telzo2000/meishi001/img/img00002.jpg

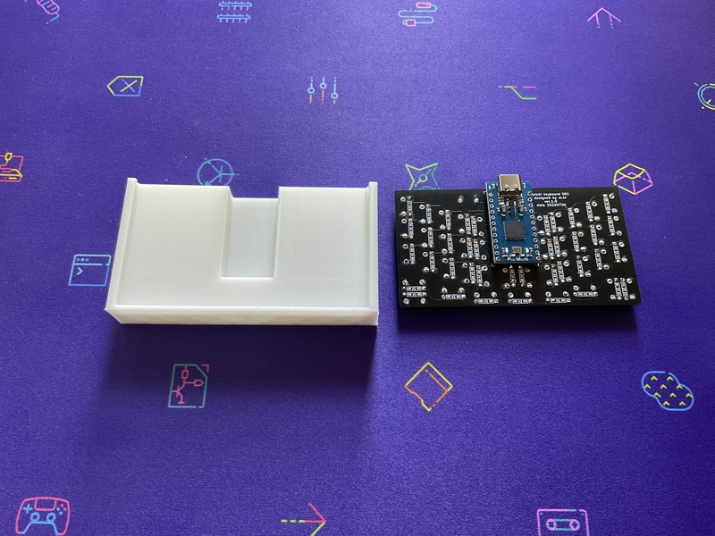
img/img00002.jpg
