telzo2000/meishi001/img/img00003.jpg

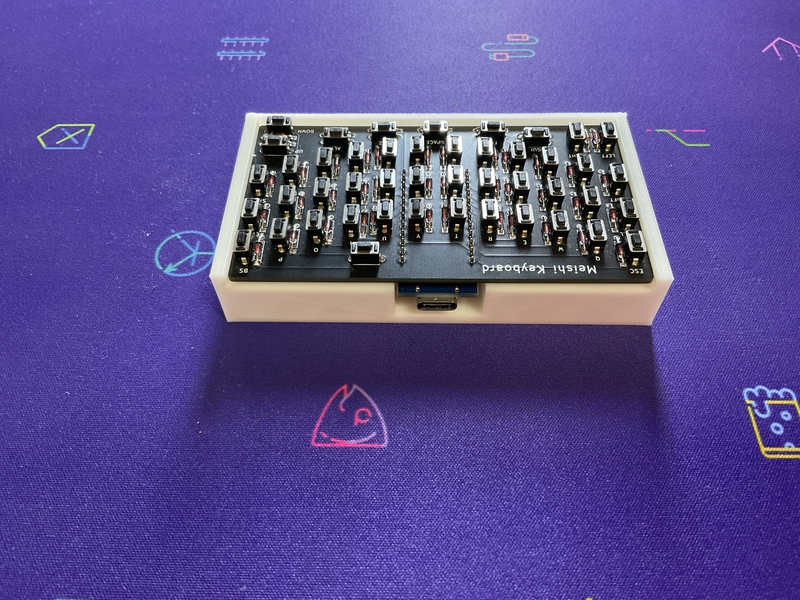
img/img00003.jpg
