telzo2000/meishi001/img/img00005.jpg

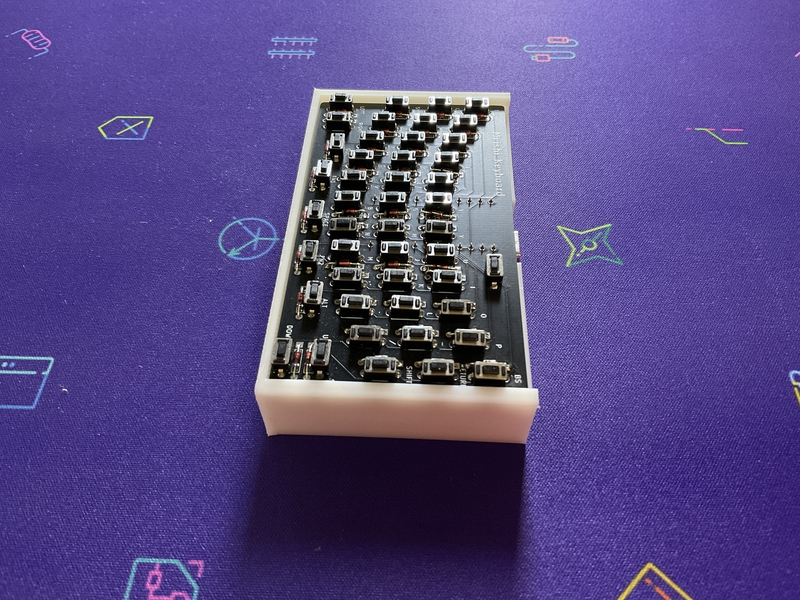
img/img00005.jpg
