telzo2000/meishi001/img/img00006.jpg

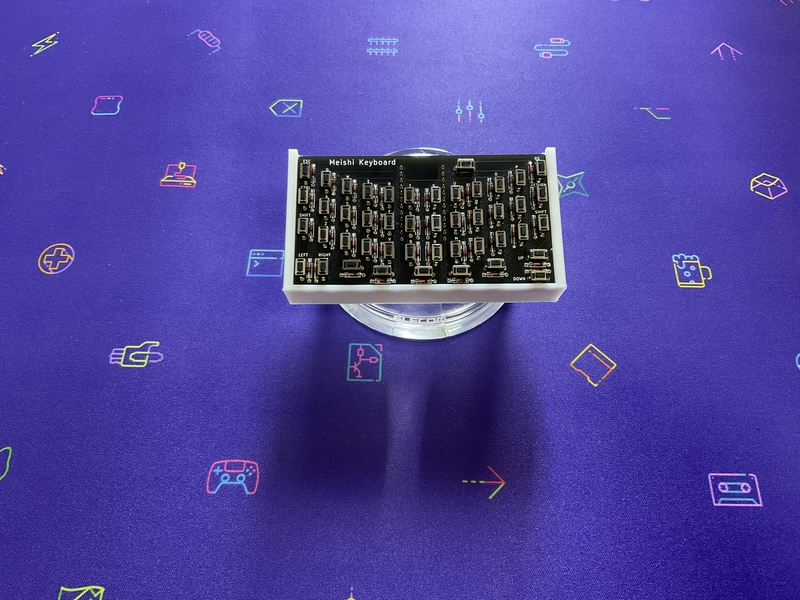
img/img00006.jpg
