telzo2000/meishi001/img/img00007.jpg

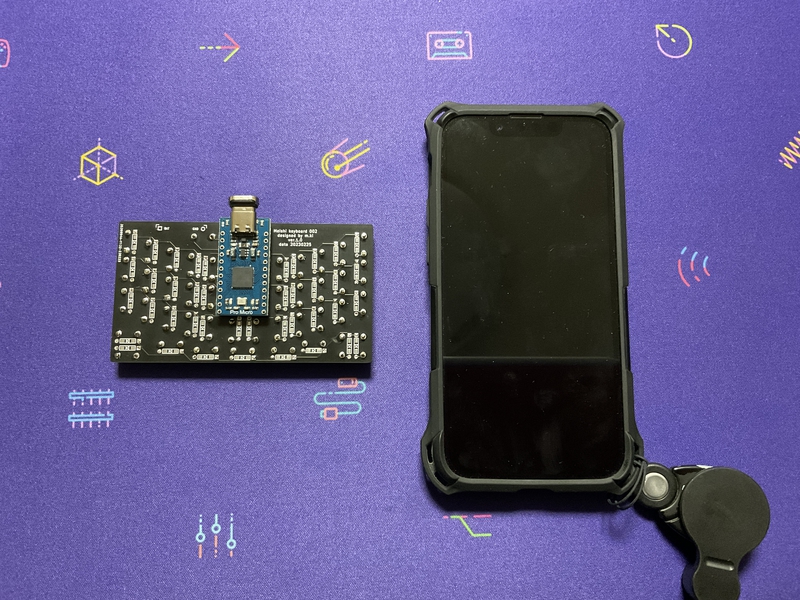
img/img00007.jpg
