telzo2000/meishi001/img/img00008.jpg

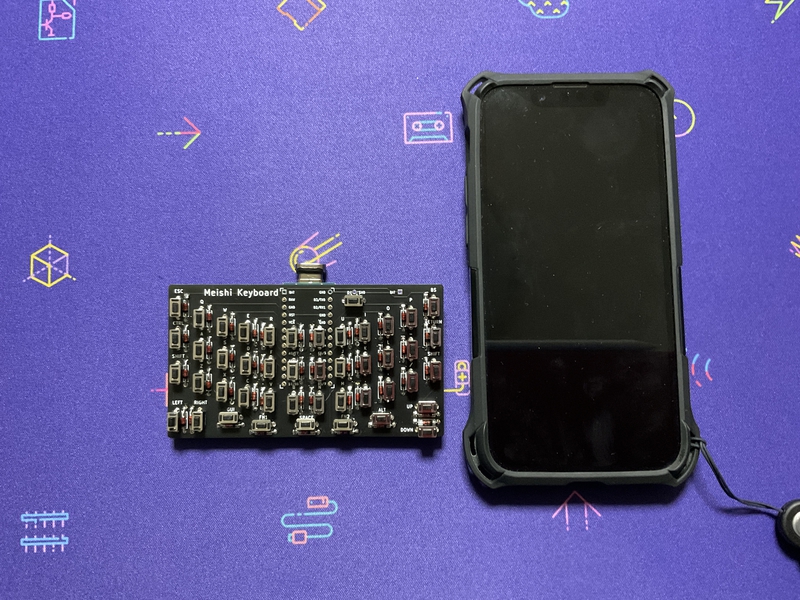
img/img00008.jpg
