telzo2000/meishi001/img/img00009.jpg

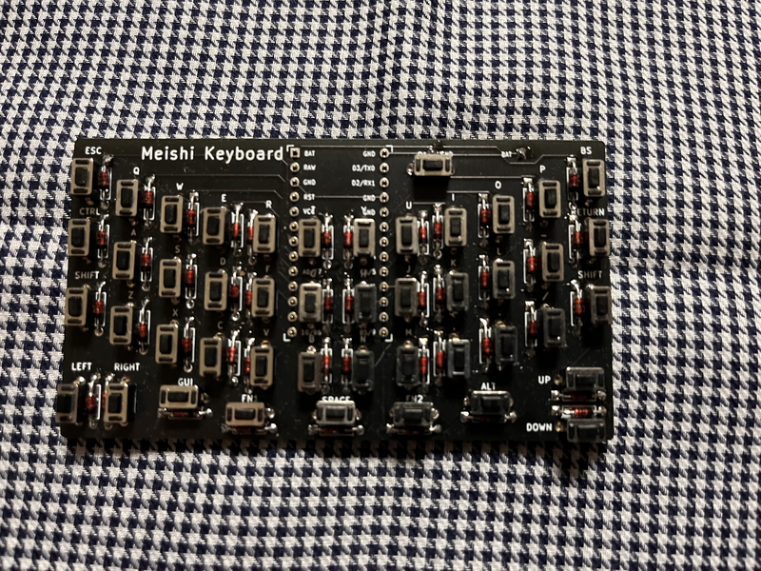
img/img00009.jpg
