telzo2000/meishi001/img/img00010.jpg

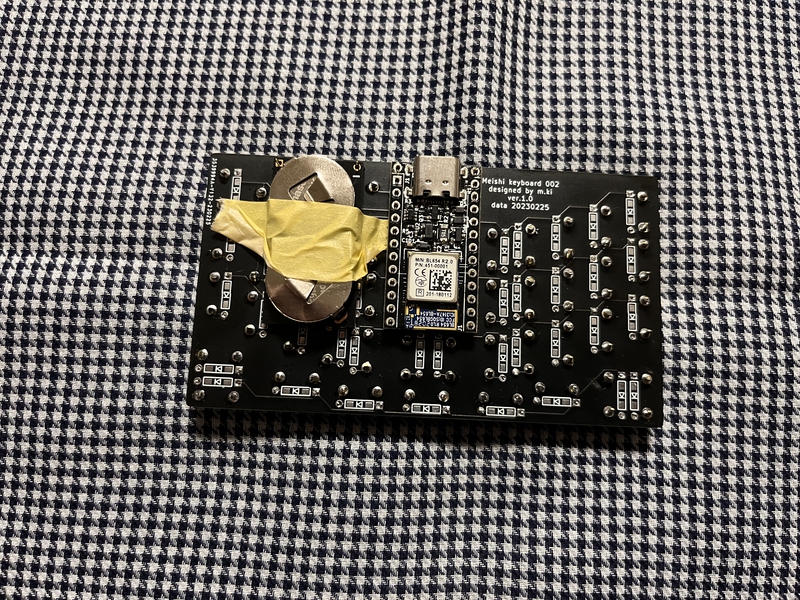
img/img00010.jpg
